gabpedroza/IDP-M208/IDP/CAD/actiatorBall Bearing.SLDASM

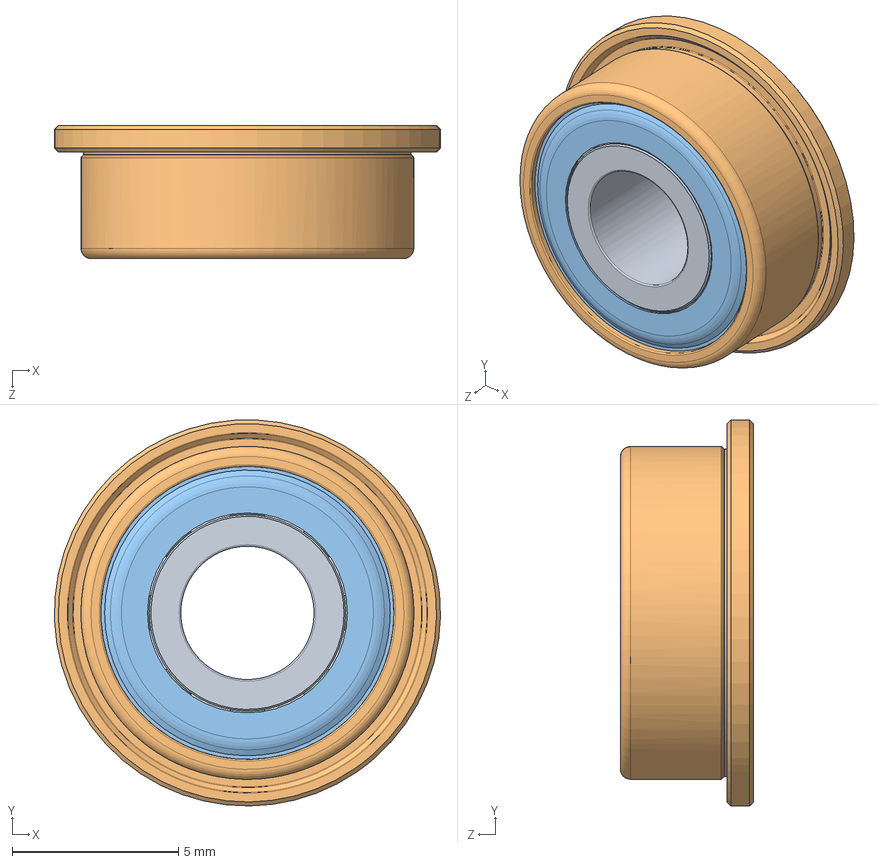
[picture p2: CAD file, 2025-11-18]
IDP/CAD/actiatorBall Bearing.SLDASM
11.6 x 11.6 x 4.00 mm
actiatorBody2 x 8
actiatorBody3 x 2
actiatorBody4
actiatorBody5
