gabpedroza/IDP-M208/IDP/CAD/actiatorBody3.SLDPRT

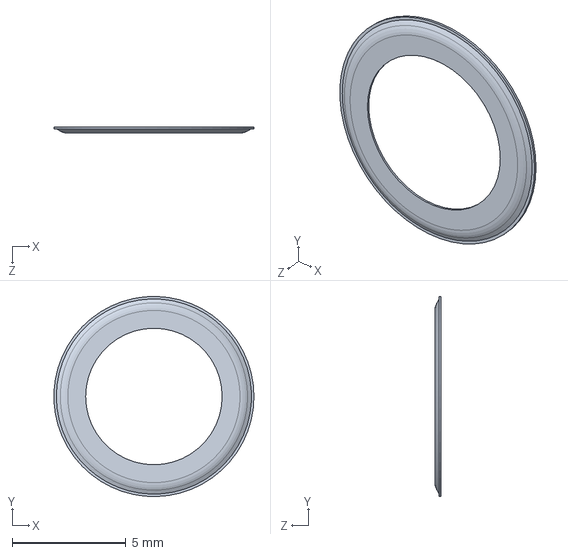
[picture p11: CAD file, 2025-11-18]
IDP/CAD/actiatorBody3.SLDPRT
8.79 x 8.80 x 0.277 mm
