gabpedroza/IDP-M208/assembly_parts/sidepieces.SLDPRT

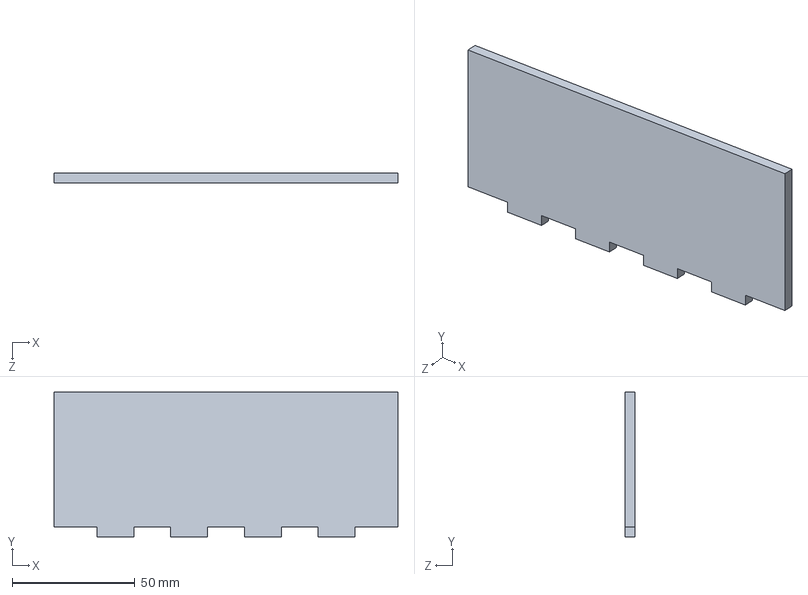
[picture p12: CAD file, 2025-11-18]
assembly_parts/sidepieces.SLDPRT
140.0 x 59.0 x 4.00 mm
