gabpedroza/IDP-M208/IDP/CAD/actiatorMotor Enclosure.SLDPRT

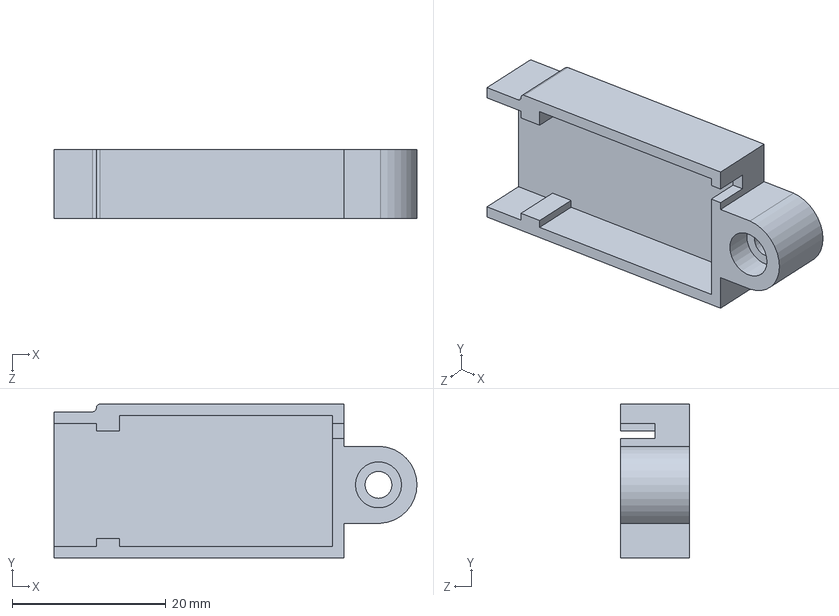
[picture p13: CAD file, 2025-11-18]
IDP/CAD/actiatorMotor Enclosure.SLDPRT
47.2 x 20.0 x 9.00 mm
