gabpedroza/IDP-M208/assembly_parts/battery slot.SLDPRT

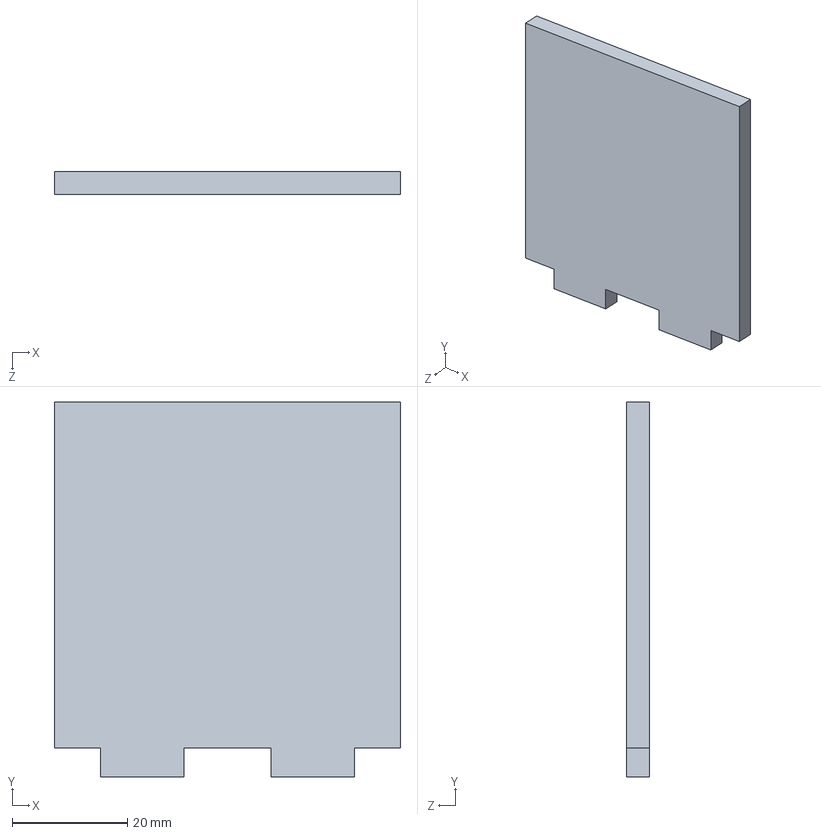
[picture p14: CAD file, 2025-11-18]
assembly_parts/battery slot.SLDPRT
60.0 x 65.0 x 4.00 mm
