gabpedroza/IDP-M208/IDP/CAD/actiatorMicroMotorN20.SLDPRT

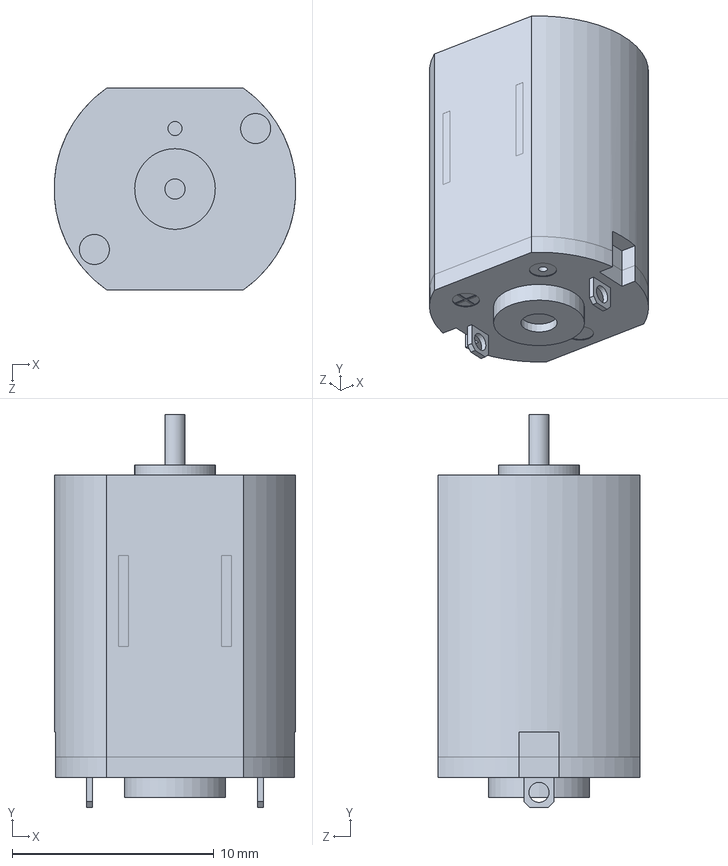
[picture p15: CAD file, 2025-11-18]
IDP/CAD/actiatorMicroMotorN20.SLDPRT
12.0 x 19.5 x 10.0 mm
