gabpedroza/IDP-M208/IDP/CAD/actiatorMicroMotorN20Suj1.SLDPRT

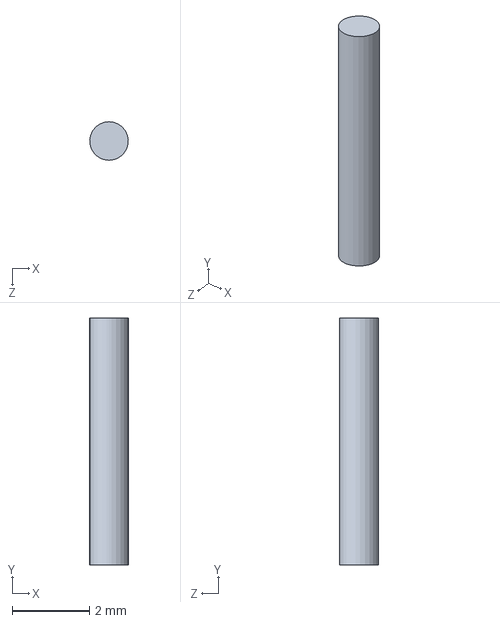
[picture p16: CAD file, 2025-11-18]
IDP/CAD/actiatorMicroMotorN20Suj1.SLDPRT
0.998 x 6.40 x 1.00 mm
