gabpedroza/IDP-M208/assembly_parts/front part.SLDPRT

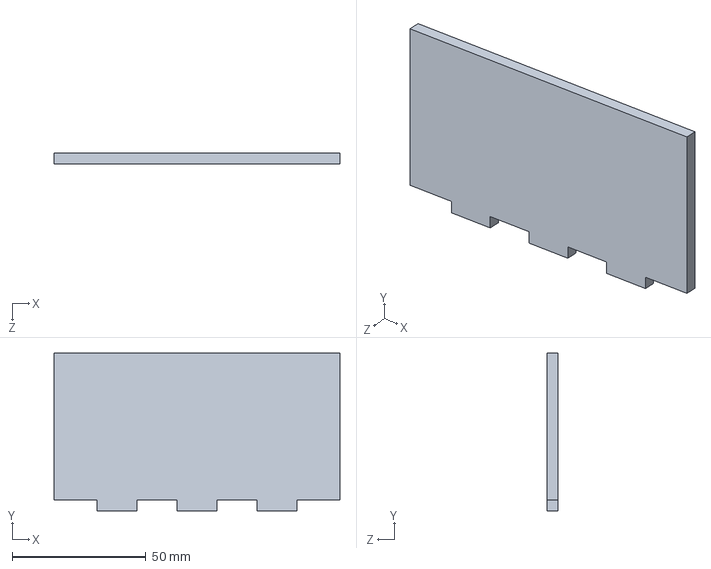
[picture p17: CAD file, 2025-11-18]
assembly_parts/front part.SLDPRT
107.0 x 59.0 x 4.00 mm
