gabpedroza/IDP-M208/IDP/CAD/actiatorMicroMotorN20Pieza2.SLDPRT

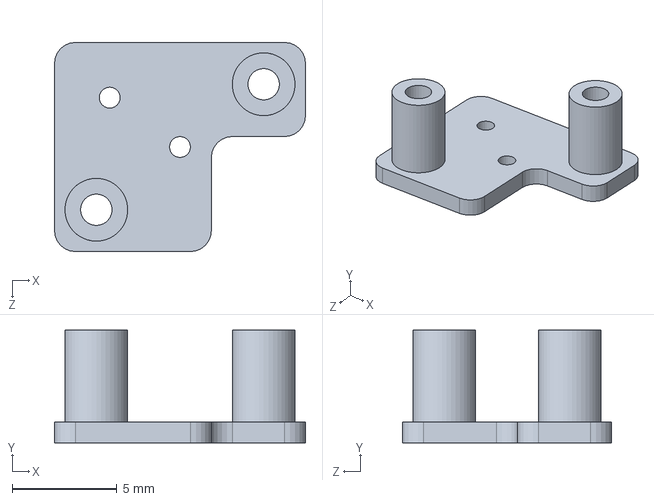
[picture p18: CAD file, 2025-11-18]
IDP/CAD/actiatorMicroMotorN20Pieza2.SLDPRT
12.0 x 5.40 x 10.0 mm
