gabpedroza/IDP-M208/IDP/CAD/actiatorMicroMotorN20Pieza3.SLDPRT

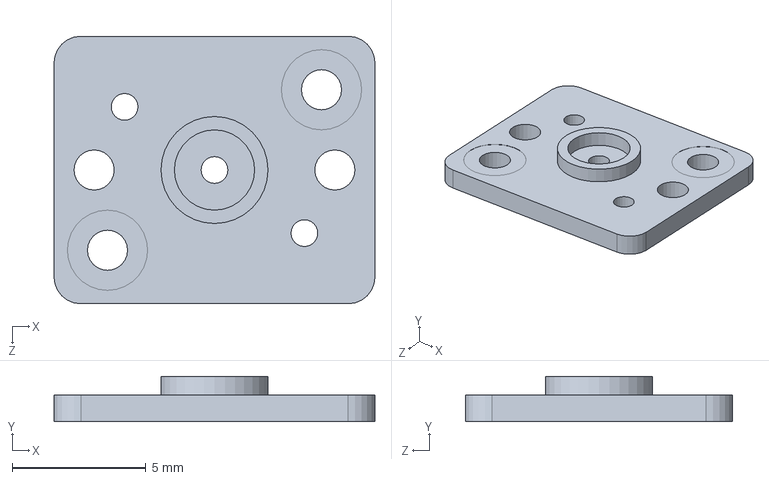
[picture p19: CAD file, 2025-11-18]
IDP/CAD/actiatorMicroMotorN20Pieza3.SLDPRT
12.0 x 1.70 x 10.0 mm
