gabpedroza/IDP-M208/IDP/CAD/ball.SLDPRT

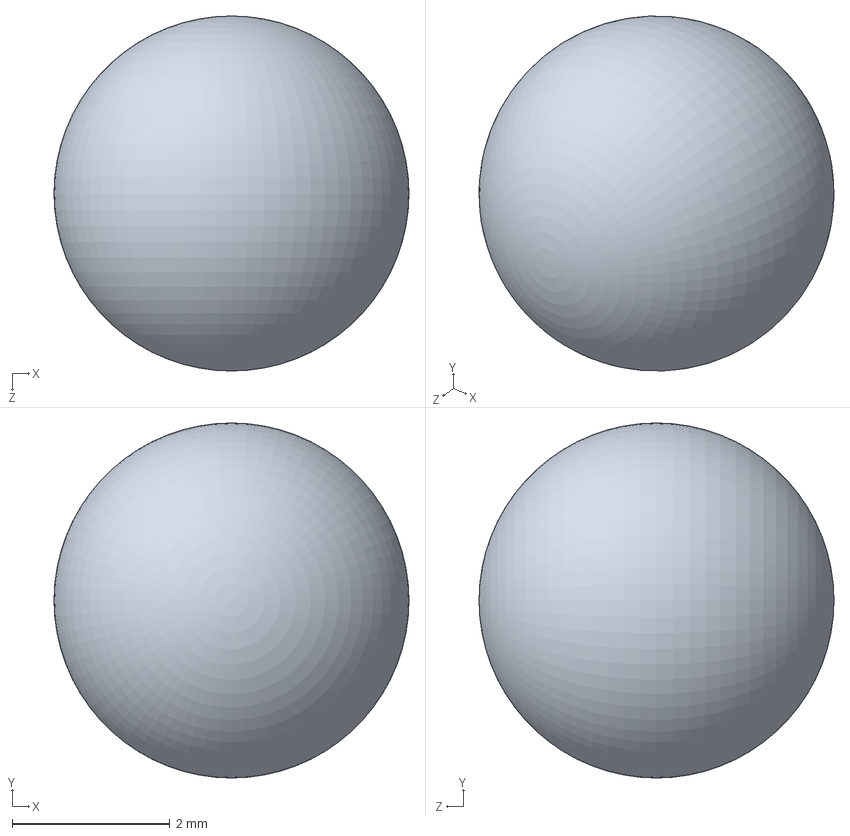
[picture p20: CAD file, 2025-11-18]
IDP/CAD/ball.SLDPRT
4.50 x 4.50 x 4.50 mm
