gabpedroza/IDP-M208/IDP/CAD/actiatorMicroMotorN20Pieza1.SLDPRT

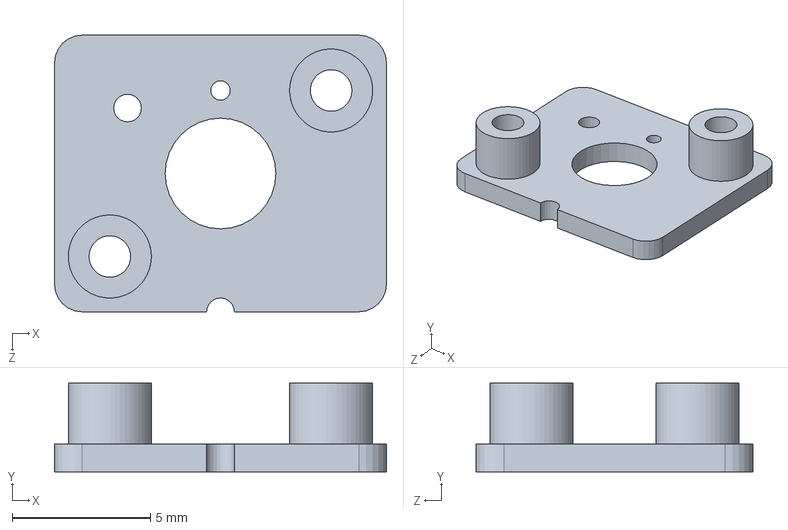
[picture p21: CAD file, 2025-11-18]
IDP/CAD/actiatorMicroMotorN20Pieza1.SLDPRT
12.0 x 3.20 x 10.0 mm
