gabpedroza/IDP-M208/IDP/CAD/actiatorBody4.SLDPRT

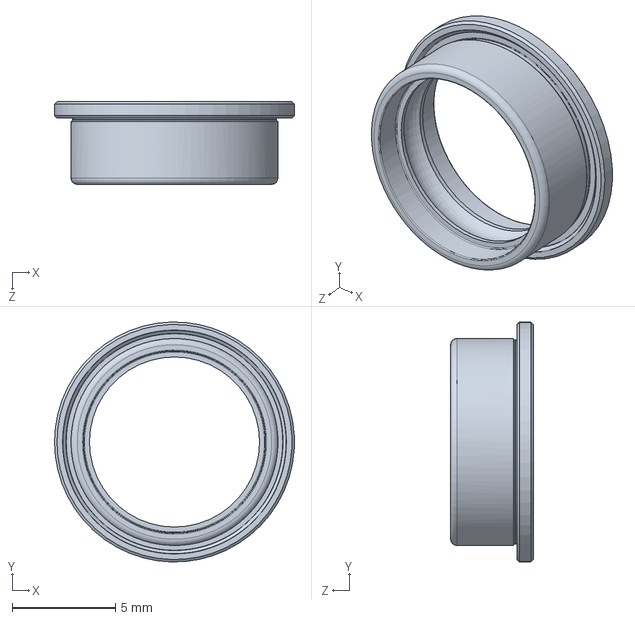
[picture p22: CAD file, 2025-11-18]
IDP/CAD/actiatorBody4.SLDPRT
11.6 x 11.6 x 4.00 mm
