gabpedroza/IDP-M208/IDP/CAD/actiatorBody2.SLDPRT

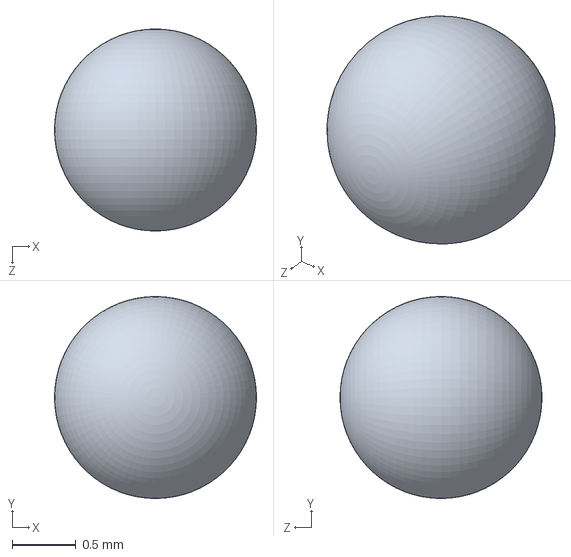
[picture p23: CAD file, 2025-11-18]
IDP/CAD/actiatorBody2.SLDPRT
1.59 x 1.59 x 1.59 mm
