gabpedroza/IDP-M208/IDP/CAD/ball_holder.SLDPRT

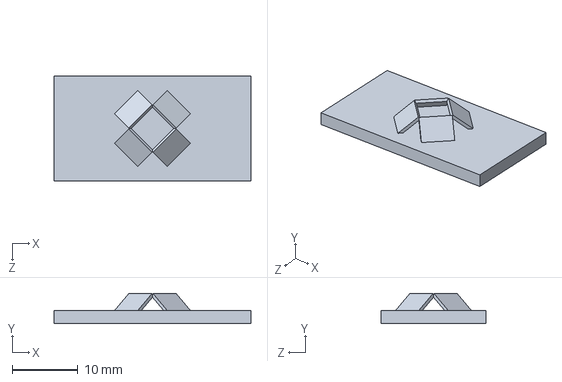
[picture p24: CAD file, 2025-11-18]
IDP/CAD/ball_holder.SLDPRT
30.0 x 4.57 x 16.0 mm
