gabpedroza/IDP-M208/IDP/CAD/actiatorShaft.SLDPRT

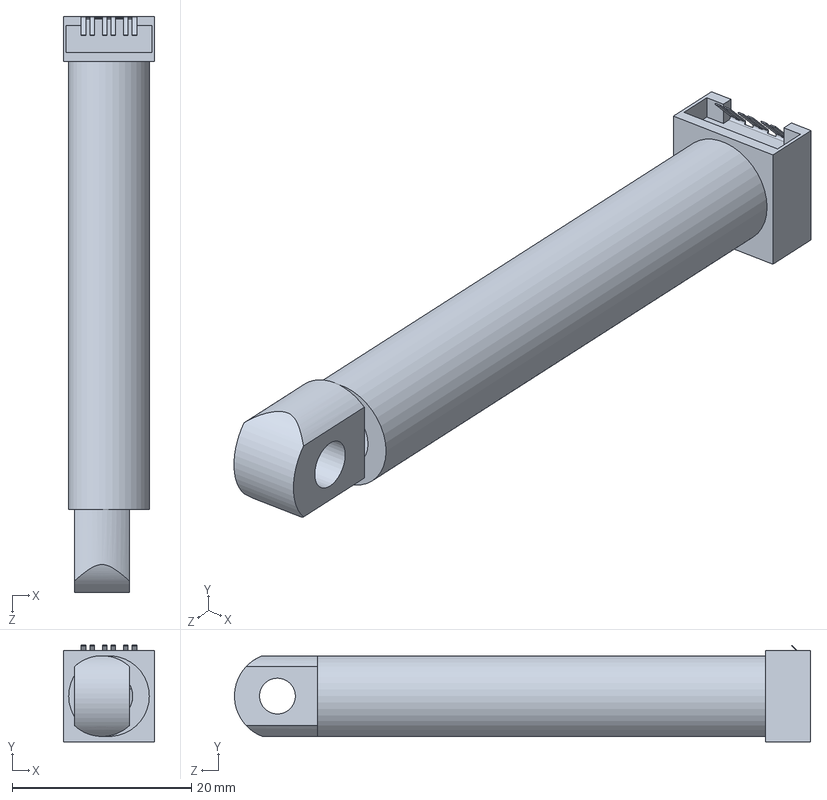
[picture p25: CAD file, 2025-11-18]
IDP/CAD/actiatorShaft.SLDPRT
10.2 x 10.8 x 64.3 mm
