gabpedroza/IDP-M208/IDP/CAD/actiatorMicroMotorN20Tornillo.SLDPRT

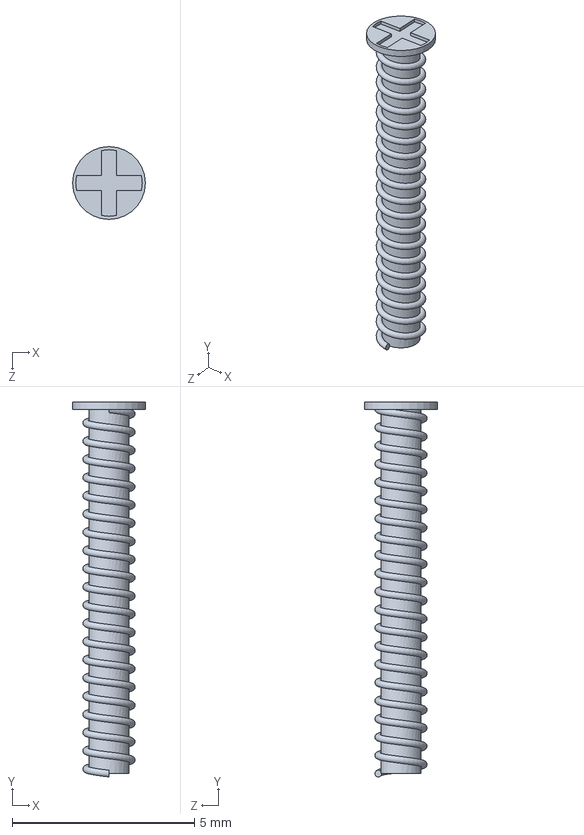
[picture p26: CAD file, 2025-11-18]
IDP/CAD/actiatorMicroMotorN20Tornillo.SLDPRT
2.00 x 10.3 x 2.00 mm
