gabpedroza/IDP-M208/IDP/CAD/actiatorShaft Enclosure.SLDPRT

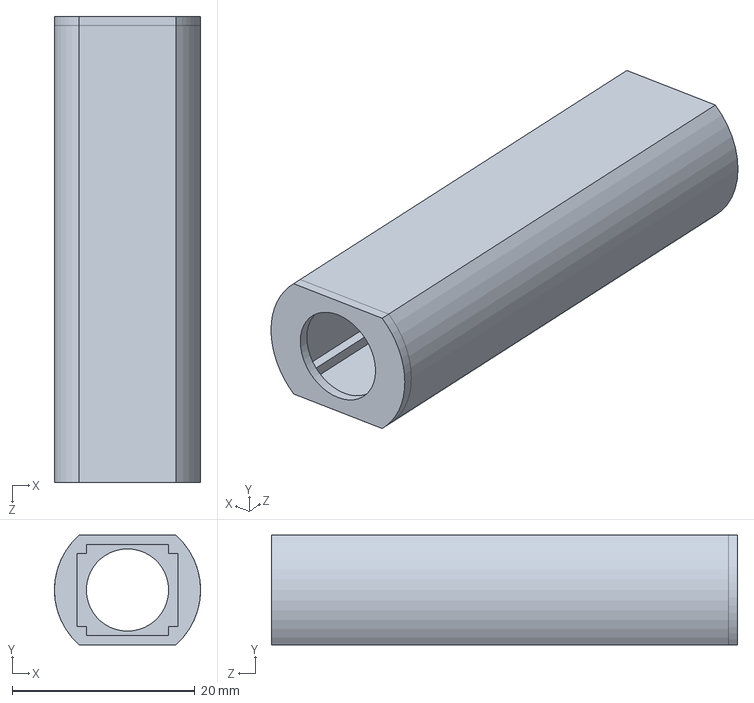
[picture p27: CAD file, 2025-11-18]
IDP/CAD/actiatorShaft Enclosure.SLDPRT
16.0 x 12.0 x 51.0 mm
