gabpedroza/IDP-M208/assembly_parts/baseassembly2.SLDASM

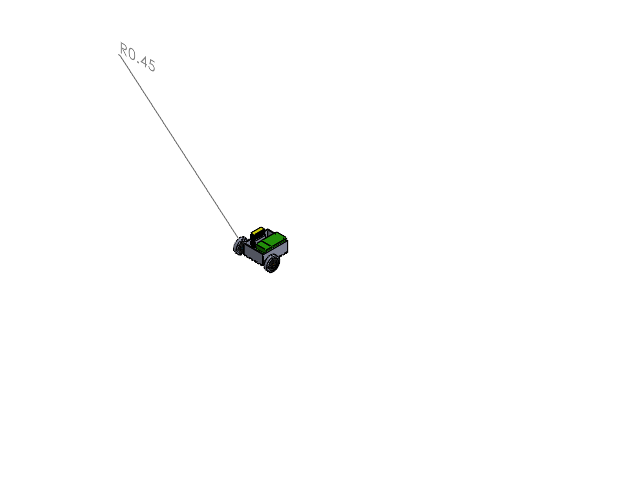
[picture p33: CAD file, 2025-11-18]
assembly_parts/baseassembly2.SLDASM
base1
new-motor-20.prt x 2
wheel_75_tyre.prt x 2
wheel_75_inner.prt x 2
sleeve.prt x 2
picobox1
battery
battery slot
sidepieces x 2
front part x 2
