gabpedroza/IDP-M208/assembly_parts/2_75_Wheel_276-1496.SLDASM

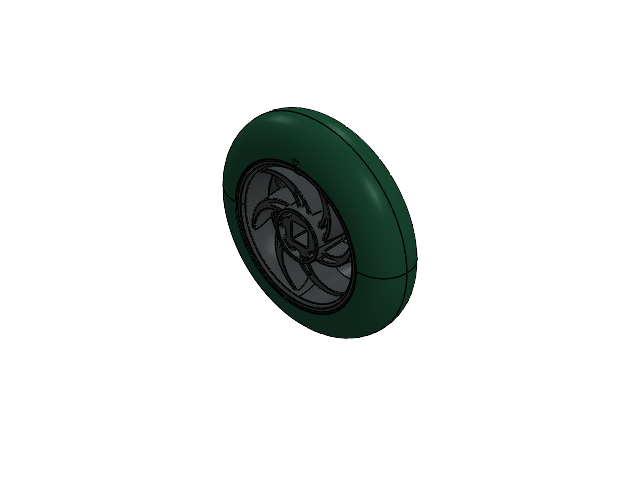
[picture p34: CAD file, 2025-11-18]
assembly_parts/2_75_Wheel_276-1496.SLDASM
276-1496-001 Rev5.STEP
276-1496-002 Rev2.STEP
276-1496-003 Rev2.STEP
