gabpedroza/IDP-M208/electronics/kicad/board_v1/board_v1.kicad_pcb

## KiCad design 02_POWER.kicad_sch

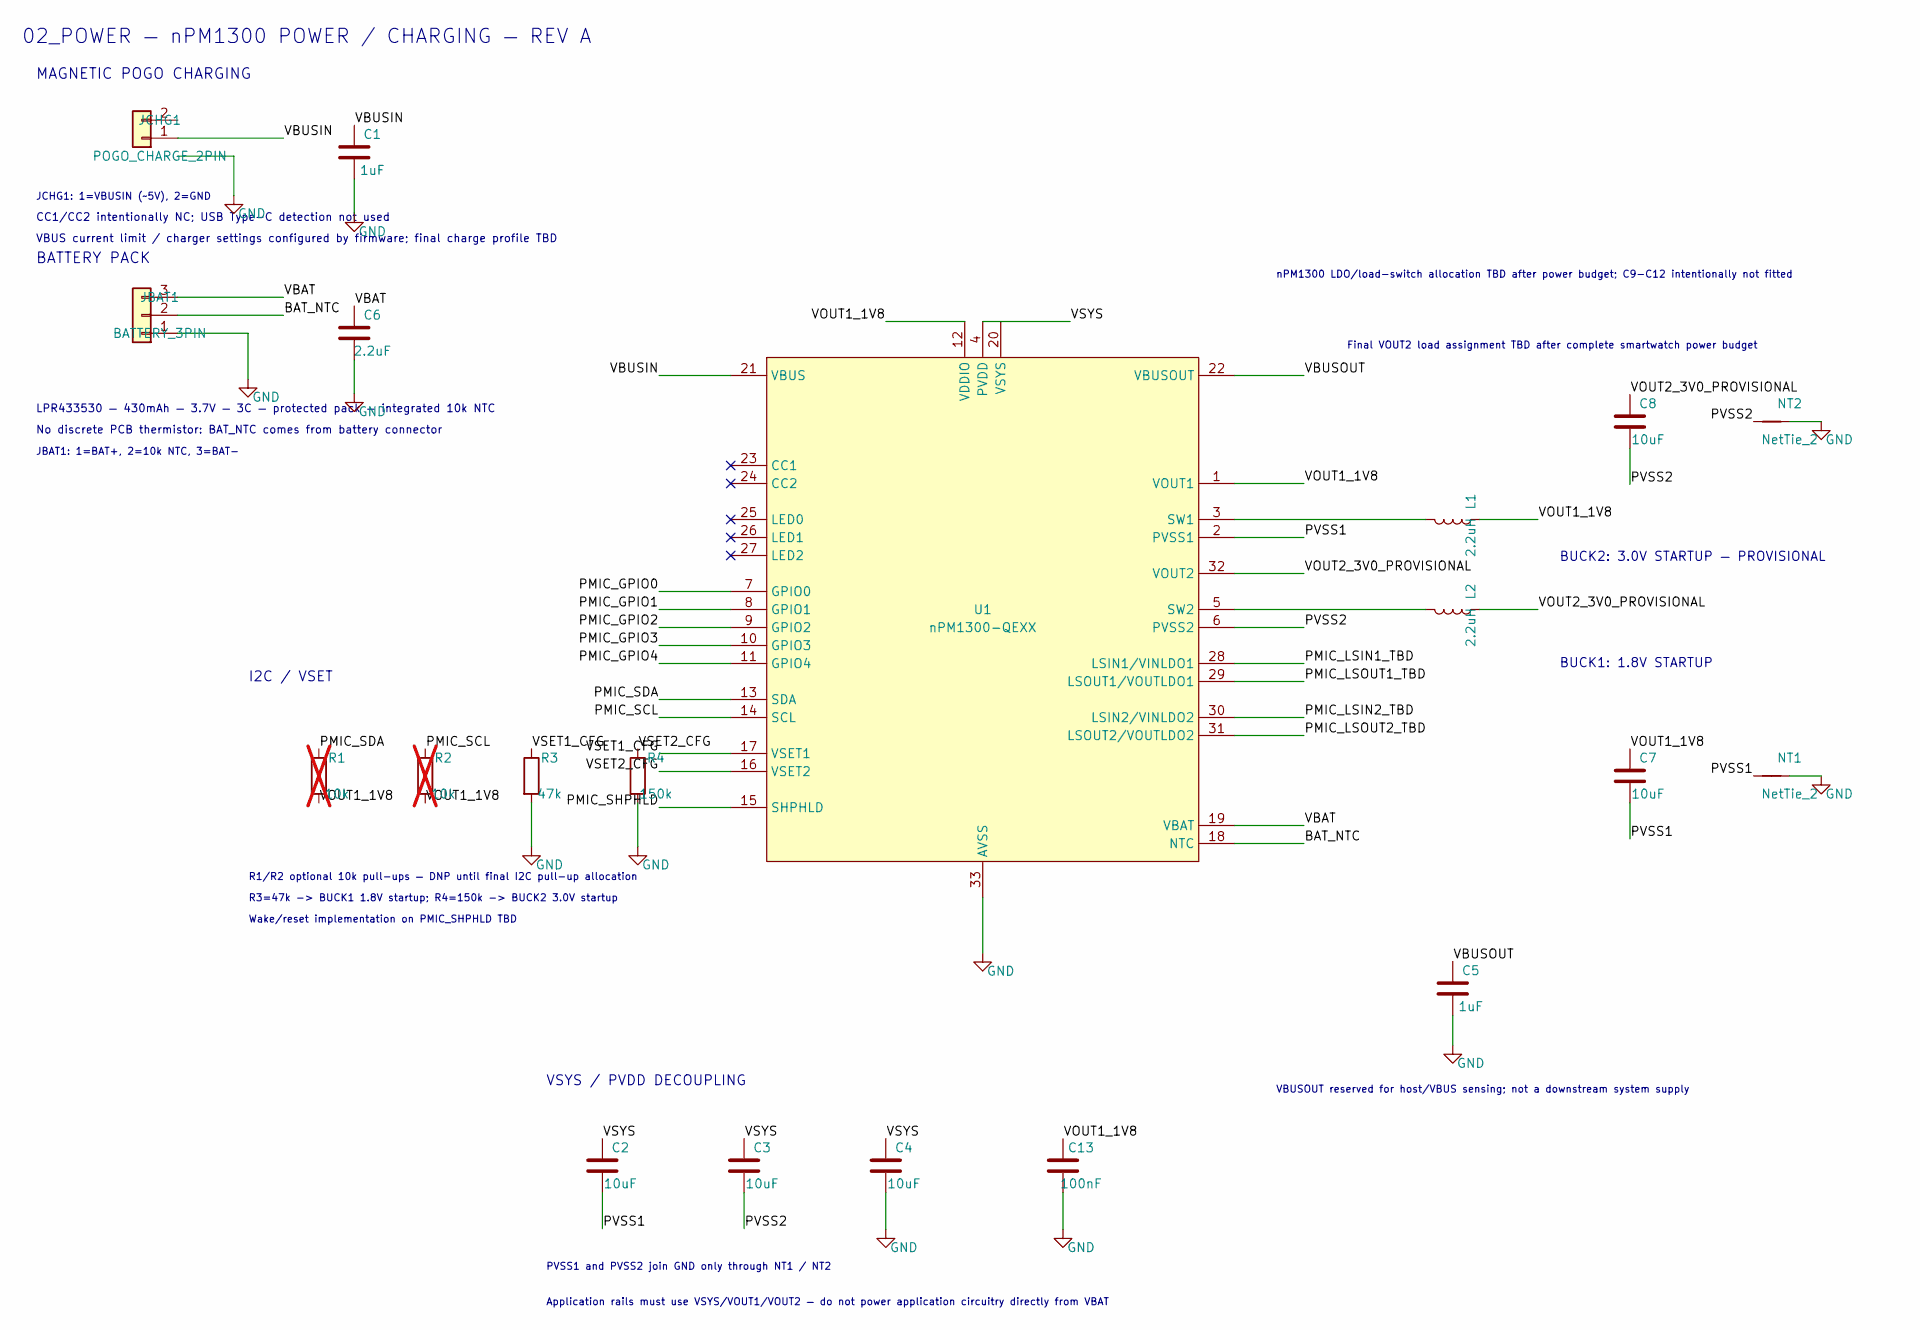
[picture p35: schematic 02_POWER.kicad_sch]

Parts:
C1, C5: 1uF
C2, C3, C4, C7, C8: 10uF
C6: 2.2uF
C13: 100nF
JBAT1: BATTERY_3PIN
JCHG1: POGO_CHARGE_2PIN
L1, L2: 2.2uH
NT1, NT2: NetTie_2
R1, R2: 10k; not fitted
R3: 47k; Tolerance 1%
R4: 150k; Tolerance 1%
U1: nPM1300-QEXX; QFN-32-1EP_5x5mm_P0.5mm_EP3.6x3.6mm_ThermalVias

Connections:
BAT_NTC: JBAT1.2, U1.18 (NTC)
GND: C1.2, C4.2, C5.2, C6.2, C13.2, JBAT1.1, NT1.2, NT2.2, R3.2, R4.2, U1.33 (AVSS)
unnamed: L1.2, U1.3 (SW1)
unnamed: L2.2, U1.5 (SW2)
PMIC_GPIO0: U1.7 (GPIO0)
PMIC_GPIO1: U1.8 (GPIO1)
PMIC_GPIO2: U1.9 (GPIO2)
PMIC_GPIO3: U1.10 (GPIO3)
PMIC_GPIO4: U1.11 (GPIO4)
PMIC_LSIN1_TBD: U1.28 (LSIN1/VINLDO1)
PMIC_LSIN2_TBD: U1.30 (LSIN2/VINLDO2)
PMIC_LSOUT1_TBD: U1.29 (LSOUT1/VOUTLDO1)
PMIC_LSOUT2_TBD: U1.31 (LSOUT2/VOUTLDO2)
PMIC_SCL: R2.1, U1.14 (SCL)
PMIC_SDA: R1.1, U1.13 (SDA)
PMIC_SHPHLD: U1.15 (SHPHLD)
PVSS1: C2.2, C7.2, NT1.1, U1.2 (PVSS1)
PVSS2: C3.2, C8.2, NT2.1, U1.6 (PVSS2)
VBAT: C6.1, JBAT1.3, U1.19 (VBAT)
VBUSIN: C1.1, JCHG1.1, U1.21 (VBUS)
VBUSOUT: C5.1, U1.22 (VBUSOUT)
VOUT1_1V8: C7.1, C13.1, L1.1, R1.2, R2.2, U1.1 (VOUT1), U1.12 (VDDIO)
VOUT2_3V0_PROVISIONAL: C8.1, L2.1, U1.32 (VOUT2)
VSET1_CFG: R3.1, U1.17 (VSET1)
VSET2_CFG: R4.1, U1.16 (VSET2)
VSYS: C2.1, C3.1, C4.1, U1.4 (PVDD), U1.20 (VSYS)

Notes on the sheet:
VBUSOUT reserved for host/VBUS sensing; not a downstream system supply
BATTERY PACK
JCHG1: 1=VBUSIN (~5V), 2=GND
VSYS / PVDD DECOUPLING
BUCK1: 1.8V STARTUP
No discrete PCB thermistor: BAT_NTC comes from battery connector
CC1/CC2 intentionally NC; USB Type-C detection not used
R3=47k -> BUCK1 1.8V startup; R4=150k -> BUCK2 3.0V startup
I2C / VSET
nPM1300 LDO/load-switch allocation TBD after power budget; C9-C12 intentionally not fitted
02_POWER — nPM1300 POWER / CHARGING — REV A
LPR433530 — 430mAh — 3.7V — 3C — protected pack — integrated 10k NTC
R1/R2 optional 10k pull-ups — DNP until final I2C pull-up allocation
MAGNETIC POGO CHARGING
JBAT1: 1=BAT+, 2=10k NTC, 3=BAT-
Wake/reset implementation on PMIC_SHPHLD TBD
VBUS current limit / charger settings configured by firmware; final charge profile TBD
Final VOUT2 load assignment TBD after complete smartwatch power budget
PVSS1 and PVSS2 join GND only through NT1 / NT2
BUCK2: 3.0V STARTUP — PROVISIONAL
Application rails must use VSYS/VOUT1/VOUT2 — do not power application circuitry directly from VBAT
