gabpedroza/IDP-M208/electronics/kicad/board_v1/board_v1.kicad_pcb

## KiCad design 07_MOTION.kicad_sch

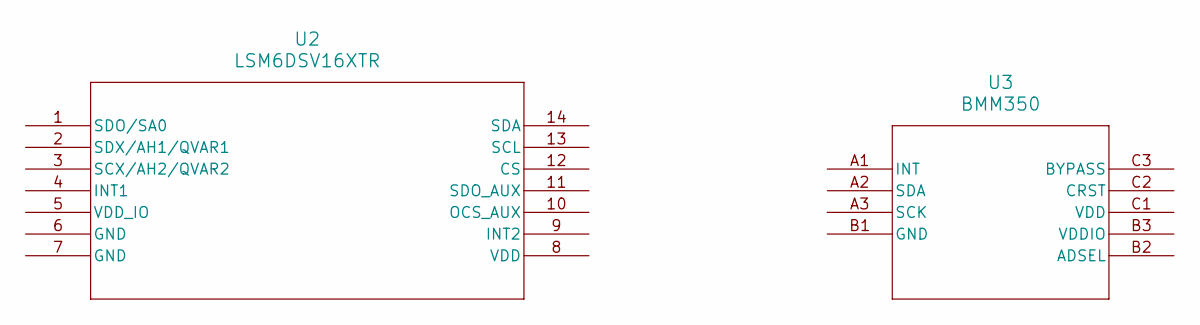
[picture p36: schematic 07_MOTION.kicad_sch]

Parts:
U2: LSM6DSV16XTR; LGA-14L_STM
U3: BMM350; BGA9_BMM350_BOS
