gabpedroza/IDP-M208/IDP/provided_example_code/sw/test_vl53l0x.py

from machine import Pin, I2C
from libs.VL53L0X.VL53L0X import VL53L0X
from utime import sleep

#good performance in box testing - use as LEFT sensor.
#no box ~350
#wall/scaffolding ~310
#box ~250-270
def test_vl53l0x():
    # config I2C Bus
    i2c_bus = I2C(id=0, sda=Pin(20), scl=Pin(21)) # I2C0 on GP8 & GP9
    print(i2c_bus.scan())  # Get the address (nb 41=0x29, 82=0x52)
    
    # Setup vl53l0 object
    vl53l0 = VL53L0X(i2c_bus)
    vl53l0.set_Vcsel_pulse_period(vl53l0.vcsel_period_type[0], 18)
    vl53l0.set_Vcsel_pulse_period(vl53l0.vcsel_period_type[1], 14)


    while True:
        print("Starting vl53l0...")

        # Start device
        vl53l0.start()

        # Read ten samples
        while True:
            distance = vl53l0.read()
            print(f"Distance = {distance}mm")  # Check calibration!
            sleep(0.5)
        
        # Stop device
        vl53l0.stop()


if __name__ == "__main__":
    test_vl53l0x()
